Anarxus-LT/Open-Source-Chronograph/Schematic/Open_Source_Chronograph-with_photodiode/Open_Source_Chronograph.kicad_pcb

## KiCad design hardware/hardware.kicad_sch

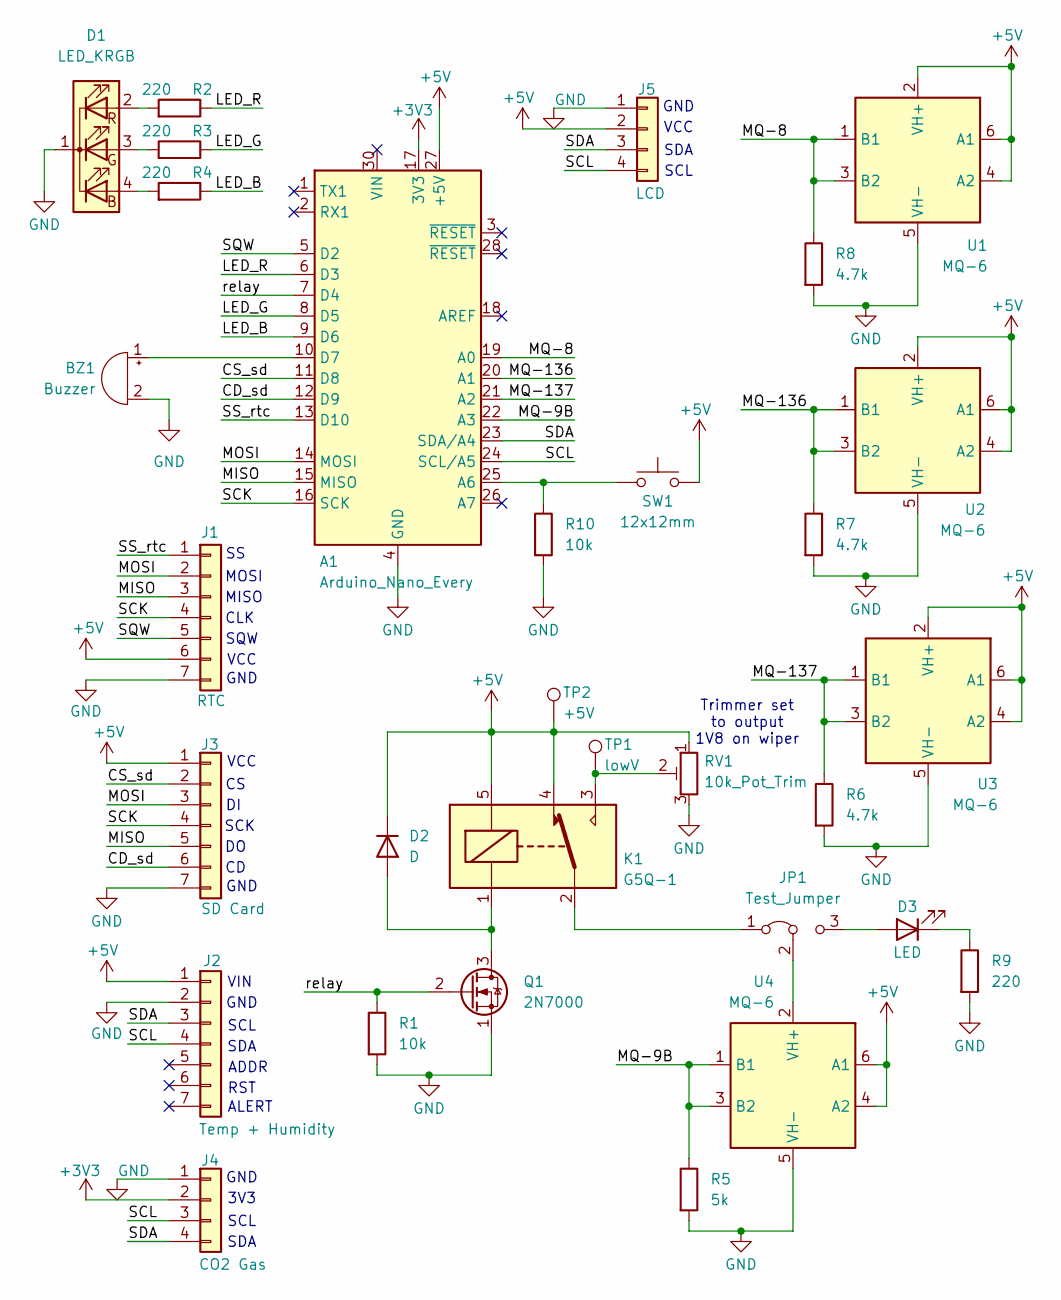
[picture p14: schematic hardware.kicad_sch]

Parts:
A1: Arduino_Nano_Every; Arduino_Nano
BZ1: Buzzer
D1: LED_KRGB
D2: D
D3: LED
J1: RTC
J2: Temp + Humidity
J3: SD Card
J4: CO2 Gas
J5: LCD
JP1: Test_Jumper
K1: G5Q-1; Relay_SPDT_Omron-G5Q-1
Q1: 2N7000; TO-92_Inline
R1, R10: 10k
R2, R3, R4, R9: 220
R5: 5k
R6, R7, R8: 4.7k
RV1: 10k_Pot_Trim
SW1: 12x12mm; Push_SMD_12x12mm; Mfg Part# EG4904TR-ND
TP1: lowV
TP2: +5V
U1, U2, U3, U4: MQ-6

Connections:
+3V3: A1.17 (3V3), J4.2
+5V: A1.27 (+5V), D2.1 (K), J1.6, J2.1, J3.1, J5.2, K1.4, K1.5, RV1.1, SW1.2, TP2.1, U1.2 (VH+), U1.4 (A2), U1.6 (A1), U2.2 (VH+), U2.4 (A2), U2.6 (A1), U3.2 (VH+), U3.4 (A2), U3.6 (A1), U4.4 (A2), U4.6 (A1)
CD_sd: A1.12 (D9), J3.6
CS_sd: A1.11 (D8), J3.2
GND: A1.4 (GND), A1.29 (GND), BZ1.2 (-), D1.1 (K), J1.7, J2.2, J3.7, J4.1, J5.1, Q1.1 (S), R1.2, R5.2, R6.2, R7.2, R8.2, R9.2, R10.2, RV1.3, U1.5 (VH-), U2.5 (VH-), U3.5 (VH-), U4.5 (VH-)
LED_B: A1.9 (D6), R4.1
LED_G: A1.8 (D5), R3.1
LED_R: A1.6 (D3), R2.1
MISO: A1.15 (MISO), J1.3, J3.5
MOSI: A1.14 (MOSI), J1.2, J3.3
MQ-8: A1.19 (A0), R8.1, U1.1 (B1), U1.3 (B2)
MQ-9B: A1.22 (A3), R5.1, U4.1 (B1), U4.3 (B2)
MQ-136: A1.20 (A1), R7.1, U2.1 (B1), U2.3 (B2)
MQ-137: A1.21 (A2), R6.1, U3.1 (B1), U3.3 (B2)
unnamed: A1.10 (D7), BZ1.1 (+)
unnamed: A1.25 (A6), R10.1, SW1.1
unnamed: D1.2 (RA), R2.2
unnamed: D1.3 (GA), R3.2
unnamed: D1.4 (BA), R4.2
unnamed: D2.2 (A), K1.1, Q1.3 (D)
unnamed: D3.1 (K), R9.1
unnamed: D3.2 (A), JP1.3 (B)
unnamed: JP1.1 (A), K1.2
unnamed: JP1.2 (C), U4.2 (VH+)
unnamed: K1.3, RV1.2, TP1.1
SCK: A1.16 (SCK), J1.4, J3.4
SCL: A1.24 (SCL/A5), J2.4, J4.3, J5.4
SDA: A1.23 (SDA/A4), J2.3, J4.4, J5.3
SQW: A1.5 (D2), J1.5
SS_rtc: A1.13 (D10), J1.1
relay: A1.7 (D4), Q1.2 (G), R1.1

Notes on the sheet:
SQW
VCC
Trimmer set to output 1V8 on wiper
ADDR
CLK
GND
VIN
SDA
SCL
SCK
RST
MISO
MOSI
ALERT
3V3
